MPRFOP/Cady02/Photo_Video/Universal-VGA-2AV-50PIN-TTL-LVDS-Controller-Board-ModuleI-LCD-AT070TN92.jpg

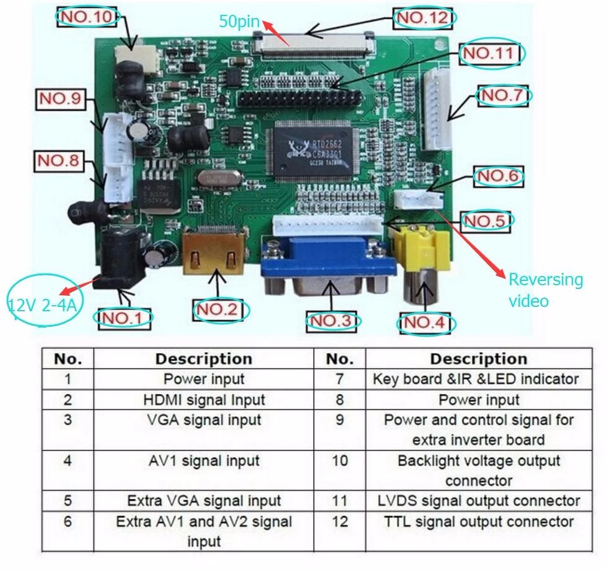
Photo_Video/Universal-VGA-2AV-50PIN-TTL-LVDS-Controller-Board-ModuleI-LCD-AT070TN92.jpg
