MPRFOP/Cady02/Photo_Video/Mein v65.png

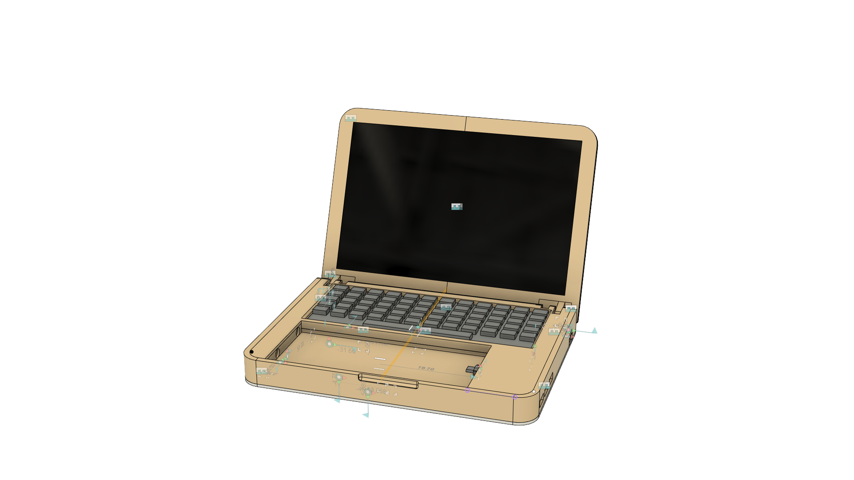
Photo_Video/Mein v65.png
