MPRFOP/Cady02/Photo_Video/Mein_2022-Mar-25_02-15-03PM-000_CustomizedView1609428317.png

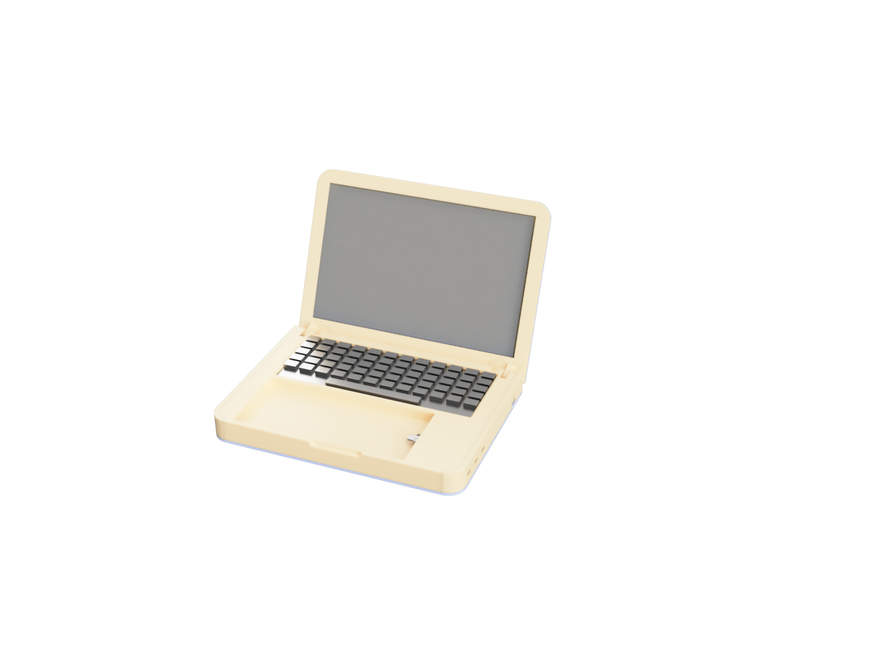
Photo_Video/Mein_2022-Mar-25_02-15-03PM-000_CustomizedView1609428317.png
