MPRFOP/Cady02/Models/3MF/DisplayCover_Top_A.3mf

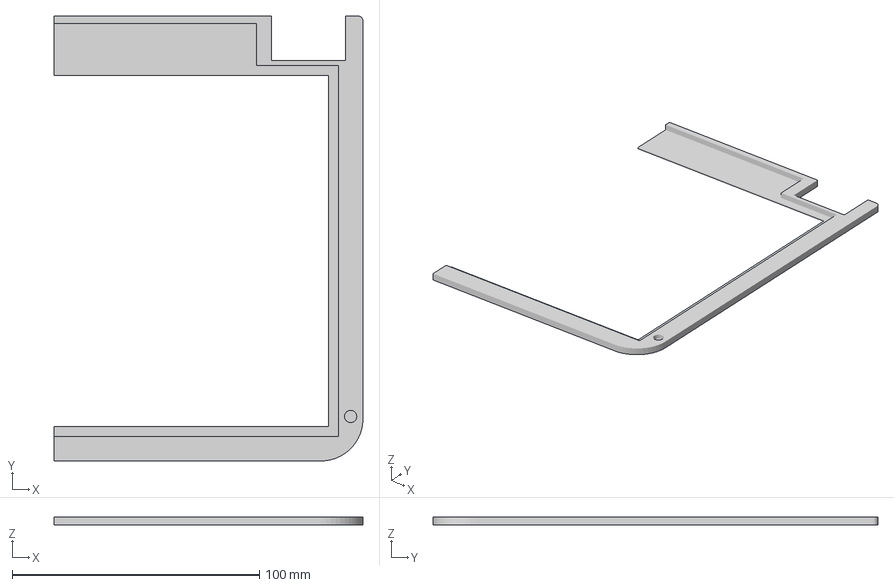
[picture p39: CAD file, 2022-03-22]
Models/3MF/DisplayCover_Top_A.3mf
125.0 x 180.0 x 3.38 mm
