MPRFOP/Cady02/Models/3MF/Holder_Phone_stand.3mf

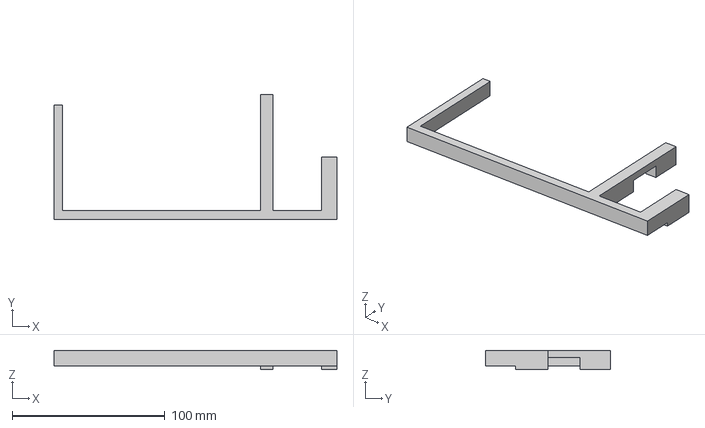
[picture p40: CAD file, 2022-03-22]
Models/3MF/Holder_Phone_stand.3mf
185.5 x 82.0 x 12.5 mm
