MPRFOP/Cady02/Models/3MF/Body_Top_B.3mf

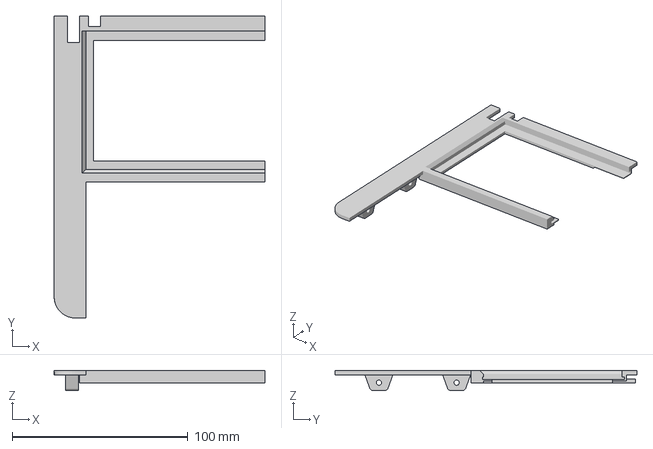
[picture p41: CAD file, 2022-03-22]
Models/3MF/Body_Top_B.3mf
120.0 x 172.0 x 11.5 mm
