MPRFOP/Cady02/Models/3MF/Holder_USBhub.3mf

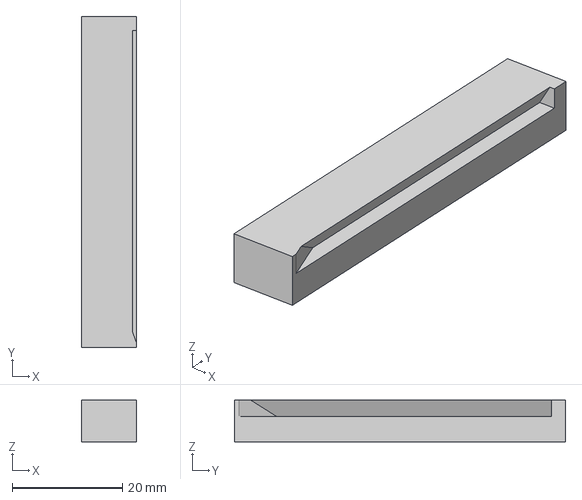
[picture p42: CAD file, 2022-03-22]
Models/3MF/Holder_USBhub.3mf
10.0 x 60.0 x 7.60 mm
