MPRFOP/Cady02/Models/3MF/Holder_Dock.3mf

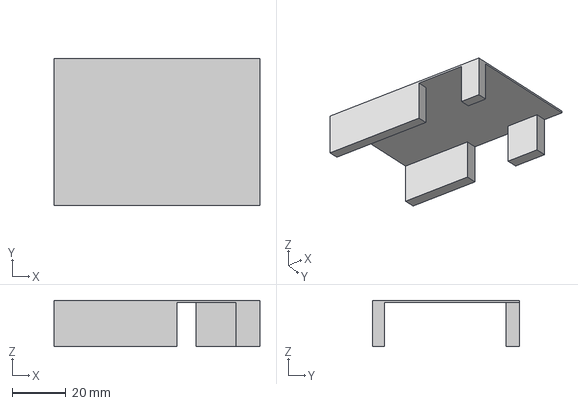
[picture p43: CAD file, 2022-03-22]
Models/3MF/Holder_Dock.3mf
77.0 x 55.0 x 17.3 mm
