MPRFOP/Cady02/Models/3MF/Body_Middle_front.3mf

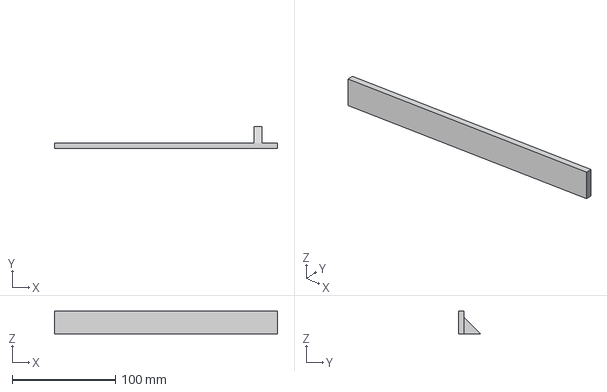
[picture p44: CAD file, 2022-03-22]
Models/3MF/Body_Middle_front.3mf
216.0 x 21.0 x 21.8 mm
