MPRFOP/Cady02/Models/3MF/Body_Middle_right.3mf

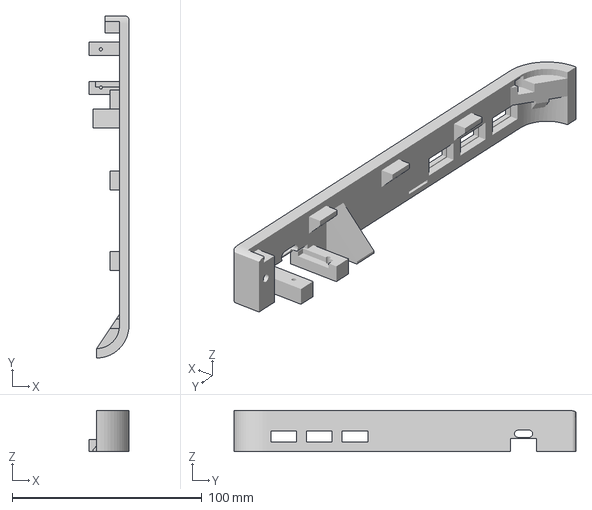
[picture p45: CAD file, 2022-03-22]
Models/3MF/Body_Middle_right.3mf
21.0 x 180.0 x 21.8 mm
