MPRFOP/Cady02/Models/3MF/Hinge_A.3mf

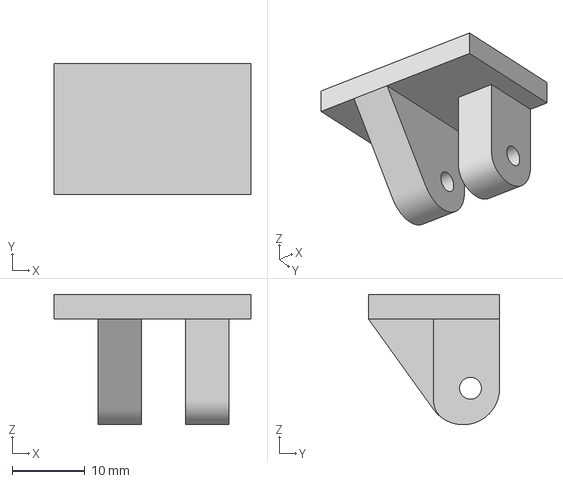
[picture p46: CAD file, 2022-03-22]
Models/3MF/Hinge_A.3mf
27.0 x 18.0 x 17.9 mm
